hbo94/CG_Scale_Olkal_SG_Mod2/Images/IMG_5636.jpg

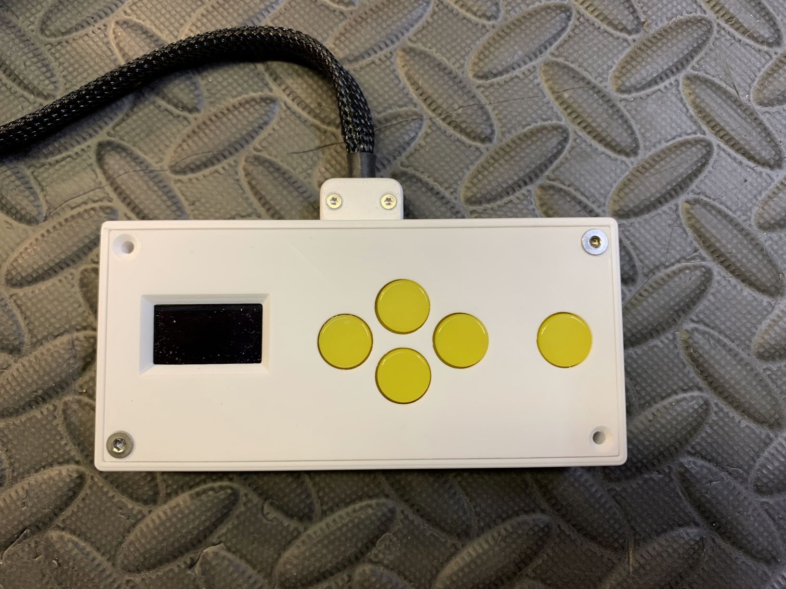
Images/IMG_5636.jpg
